LincaMarius/ISAP-1_Schematic/Pictures/Figure7.png

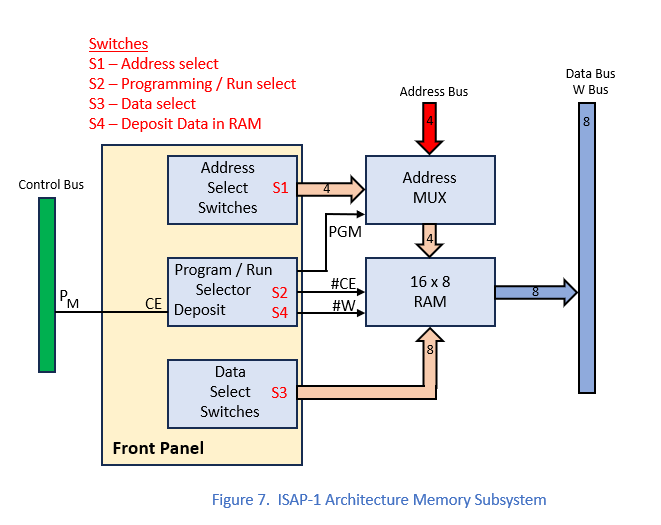
Pictures/Figure7.png
