LincaMarius/ISAP-1_Schematic/Pictures/Figure8.png

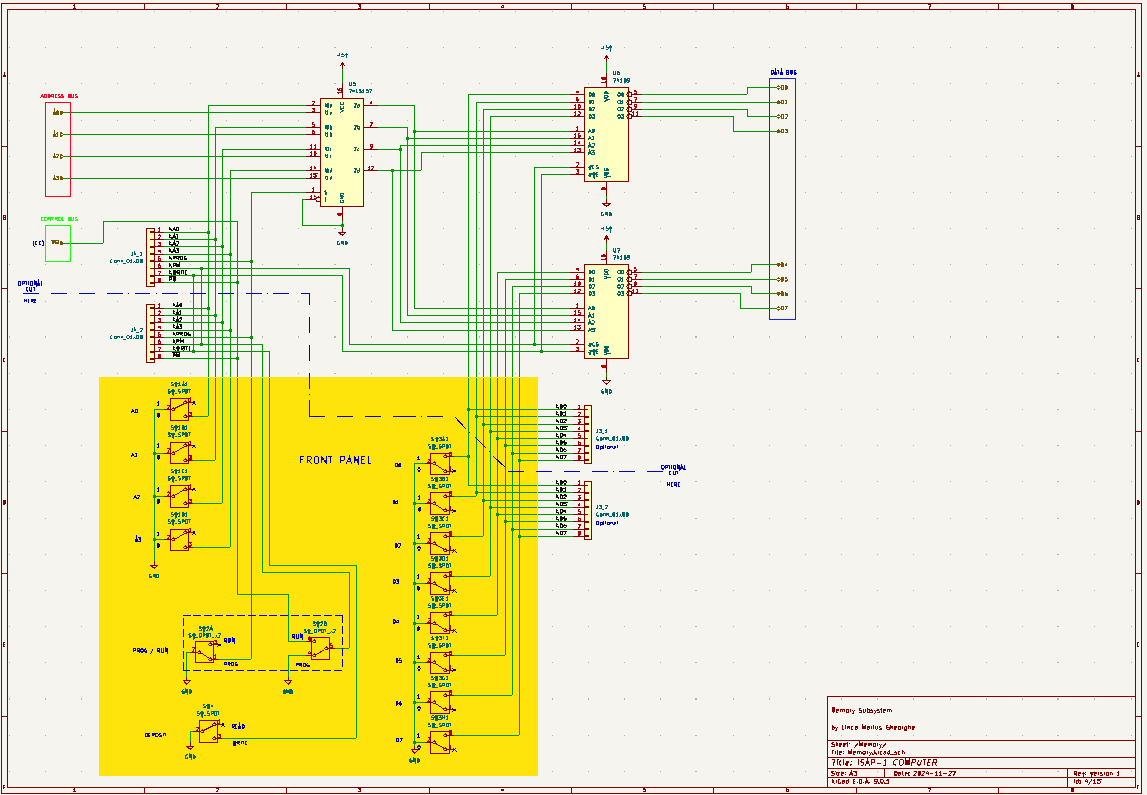
Pictures/Figure8.png
